mungewell/pico-timecode/docs/pics/7seg-blur.png

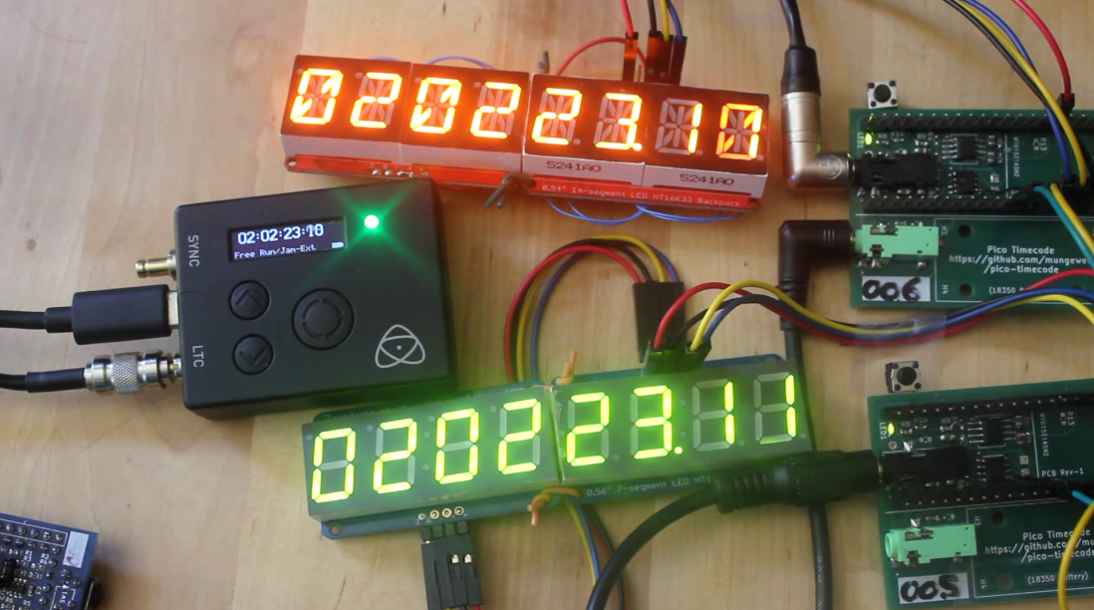
docs/pics/7seg-blur.png
