mungewell/pico-timecode/docs/pics/clockdiv_values.png

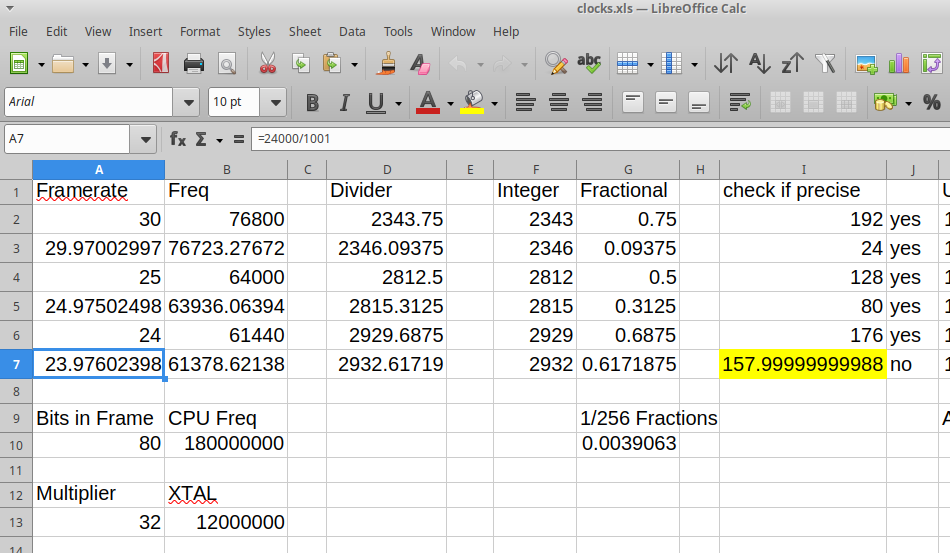
docs/pics/clockdiv_values.png
