mungewell/pico-timecode/docs/pics/digi-slate.png

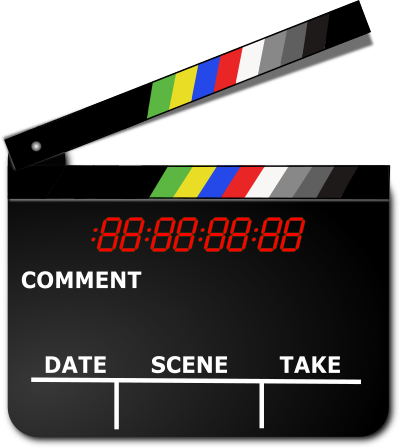
docs/pics/digi-slate.png
