mungewell/pico-timecode/docs/pics/dither_divider.png

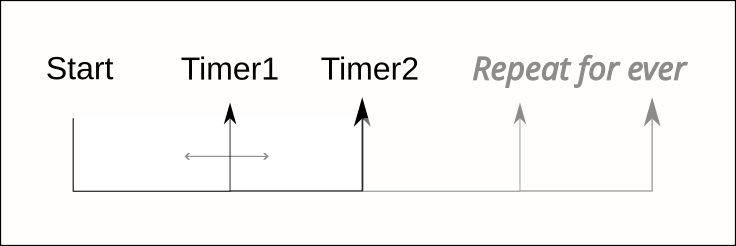
docs/pics/dither_divider.png
