mungewell/pico-timecode/docs/pics/FIFO.png

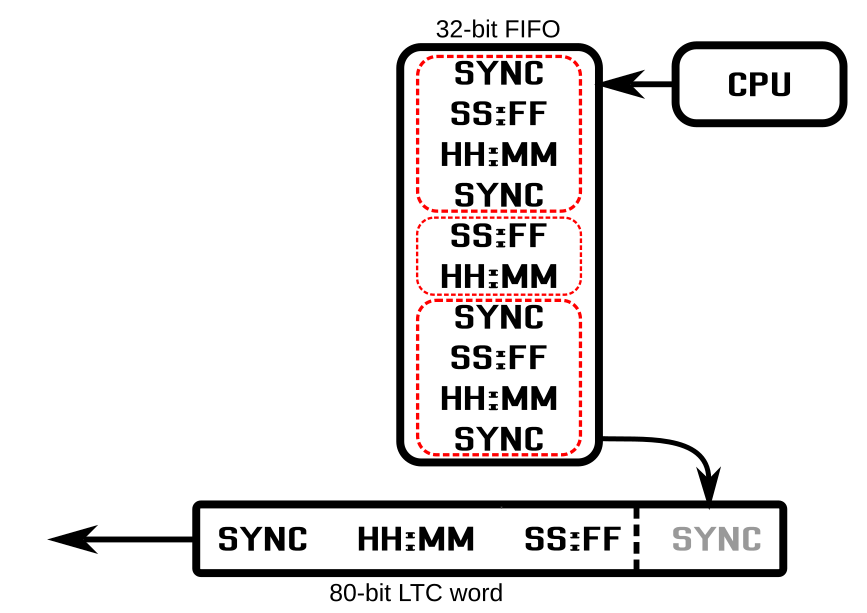
docs/pics/FIFO.png
