mungewell/pico-timecode/docs/pics/first_decode.PNG

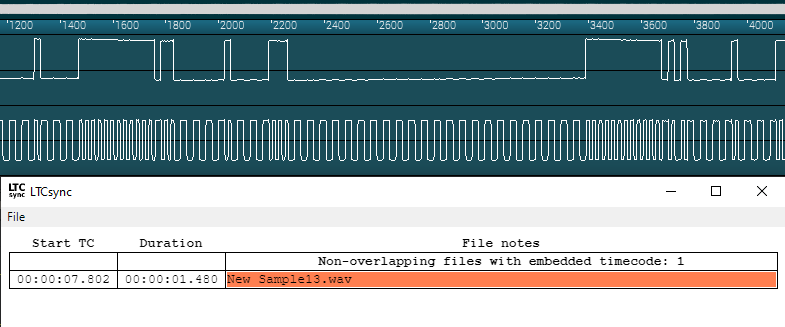
docs/pics/first_decode.PNG
