mungewell/pico-timecode/docs/pics/PI-6_display.jpg

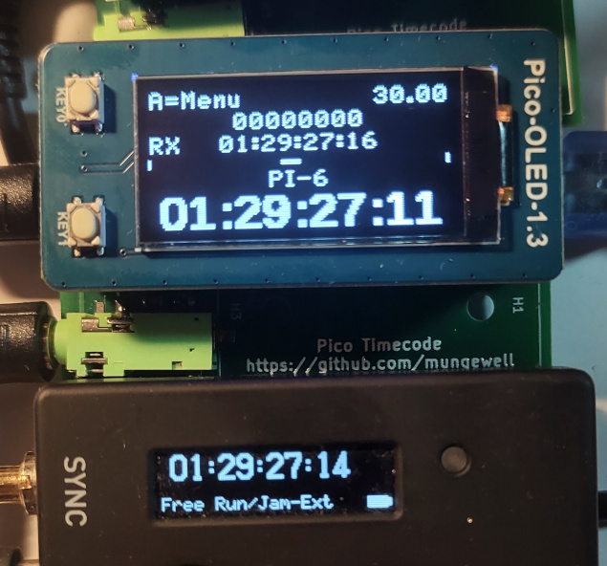
docs/pics/PI-6_display.jpg
