mungewell/pico-timecode/docs/pics/pico-1.3-oled.png

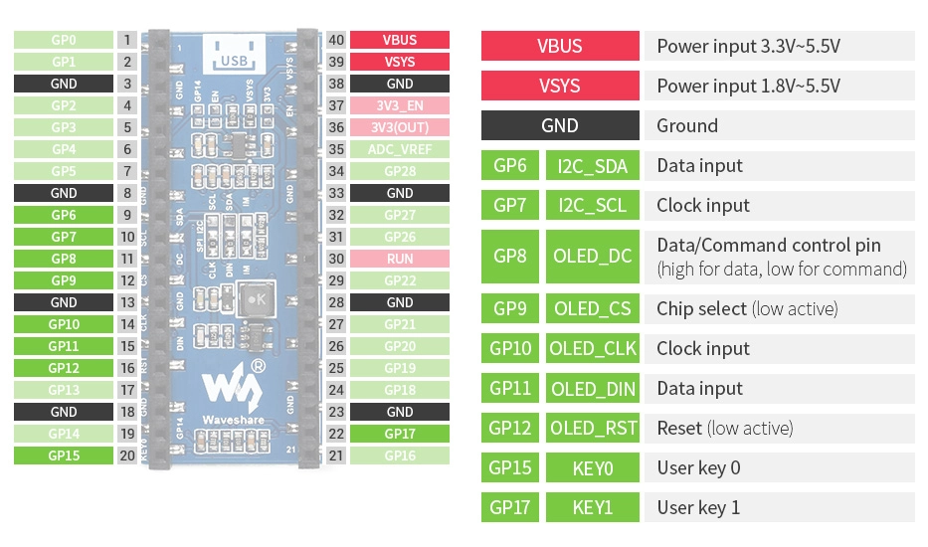
docs/pics/pico-1.3-oled.png
