mungewell/pico-timecode/docs/pics/pt_ghetto.png

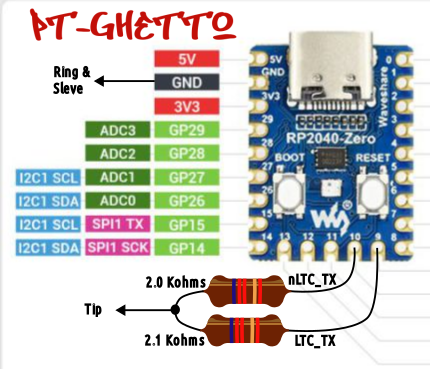
docs/pics/pt_ghetto.png
