mungewell/pico-timecode/docs/pics/temp_vs_cal_ttyACM0.png

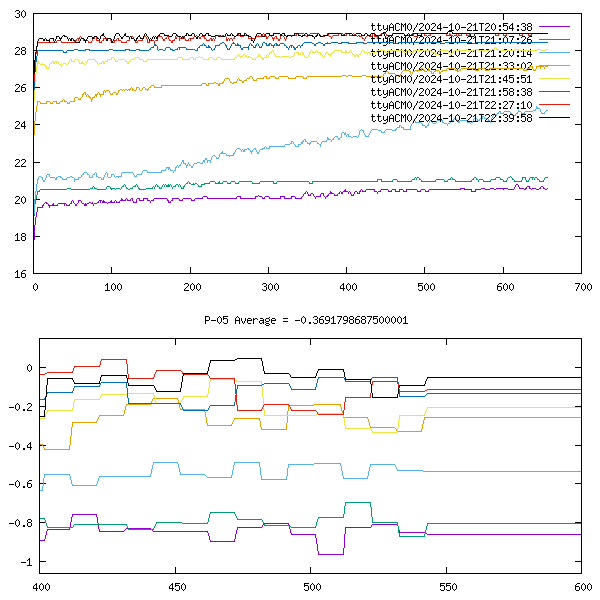
docs/pics/temp_vs_cal_ttyACM0.png
