mungewell/pico-timecode/docs/pics/XTAL_comparison.png

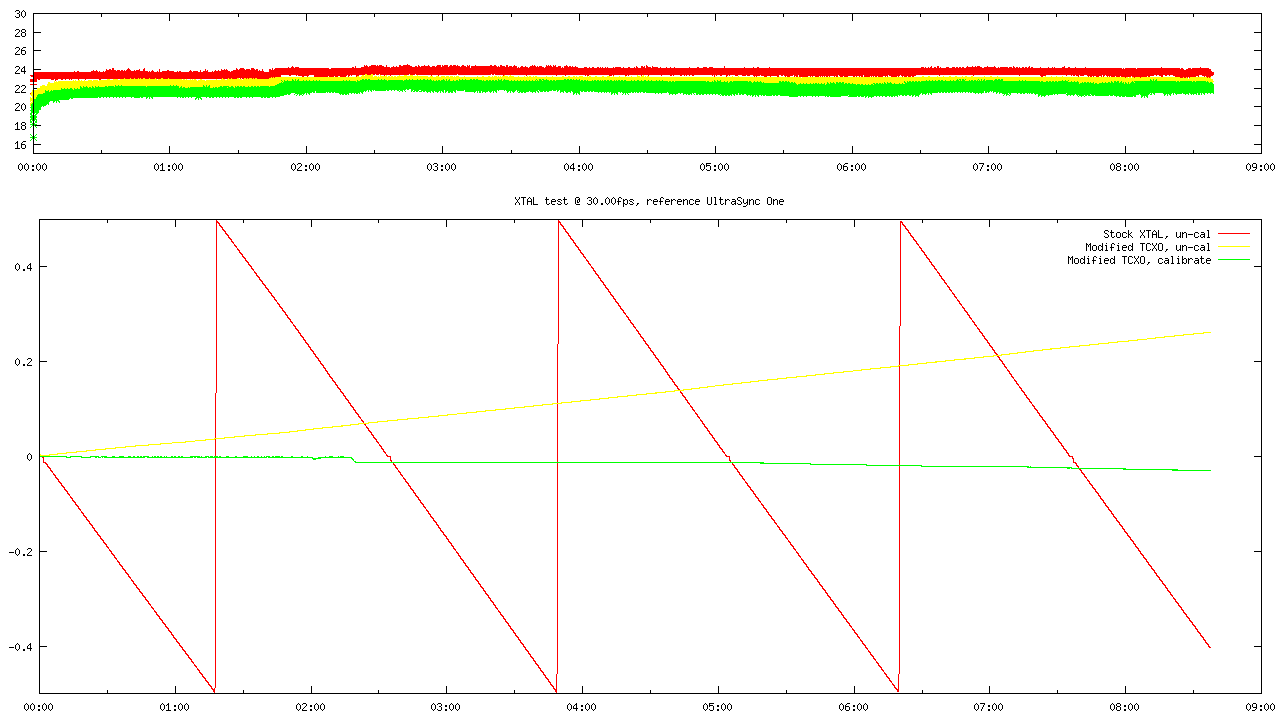
docs/pics/XTAL_comparison.png
