mungewell/pico-timecode/docs/pics/calibration_accuracy.png

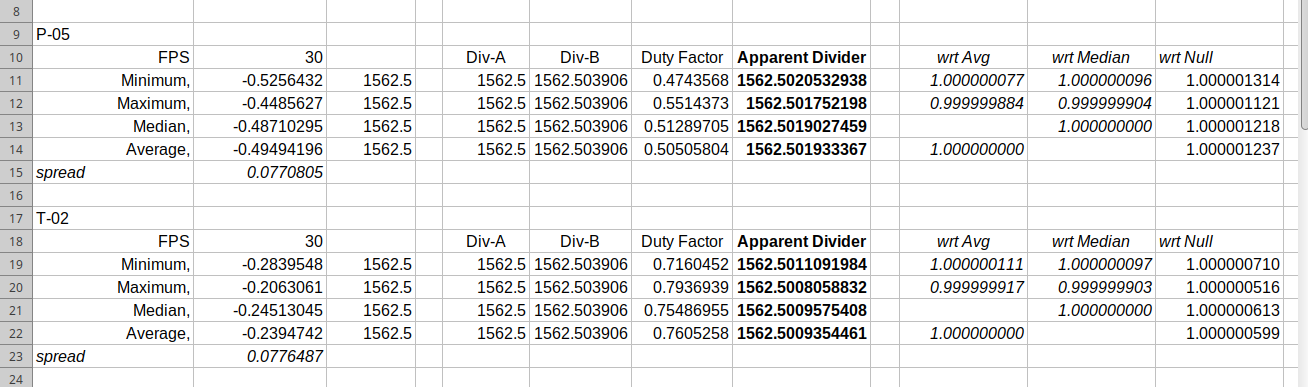
docs/pics/calibration_accuracy.png
