mungewell/pico-timecode/docs/pics/test_equipment2.png

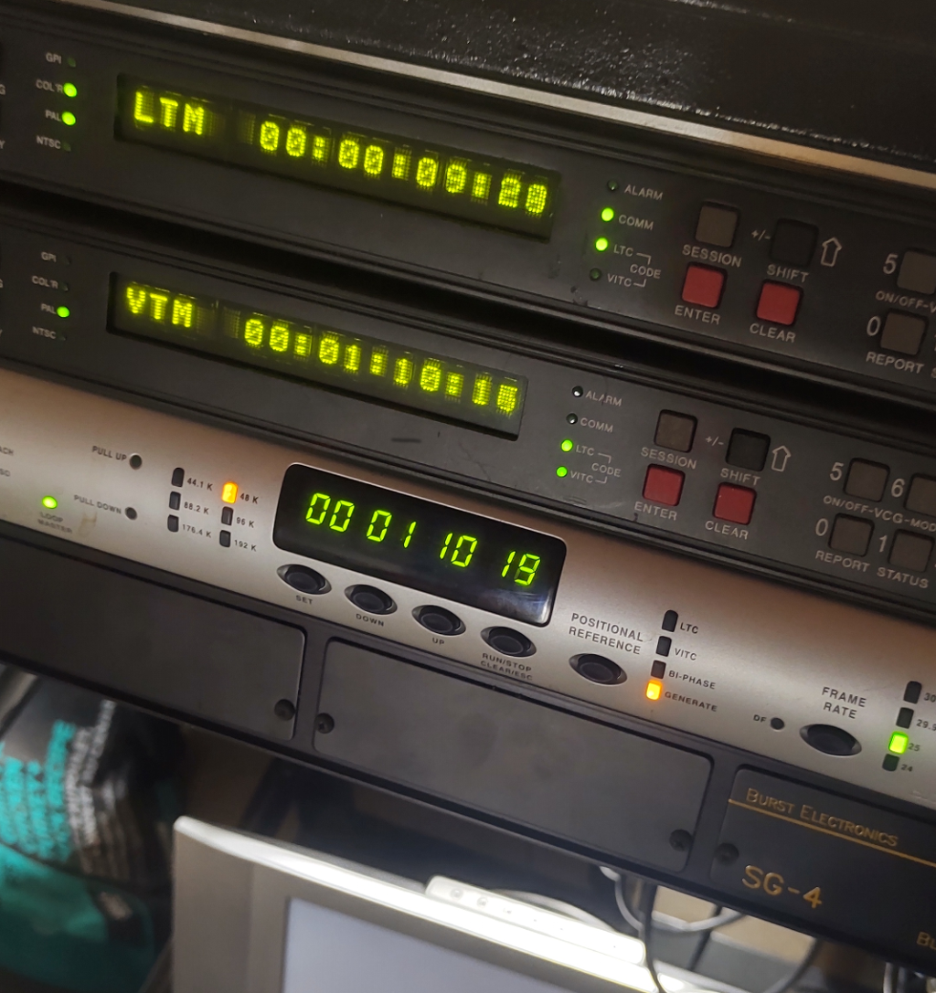
docs/pics/test_equipment2.png
