mungewell/pico-timecode/docs/pics/test_equipment.png

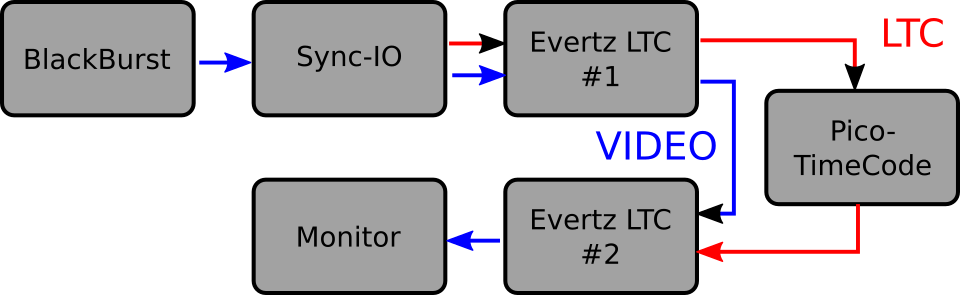
docs/pics/test_equipment.png
