mungewell/pico-timecode/docs/pics/test_rack.jpg

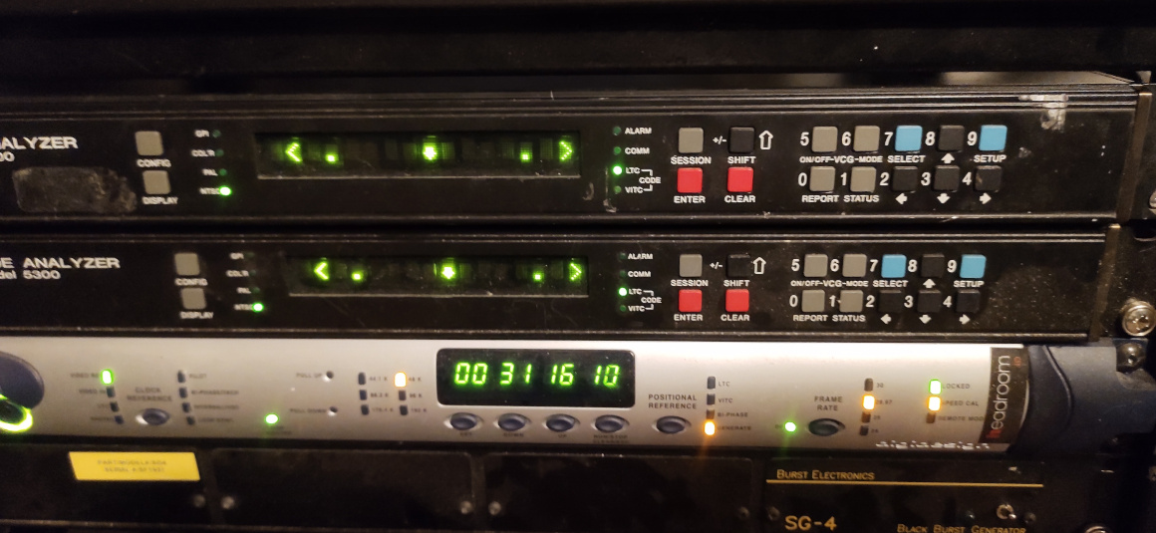
docs/pics/test_rack.jpg
